crimpdeq/crimpdeq-firmware/src/hx711.rs

/// HX711 driver
///
/// A driver for the HX711 24-bit ADC commonly used with load cells.
/// This driver provides functions for reading data, calibration, and taring.
///
/// Based on [loadcell] crate.
///
/// [loadcell]: https://crates.io/crates/loadcell
use core::fmt;

use defmt::{debug, error, info, warn};
use embassy_time::{Duration, with_timeout};
use embedded_hal::delay::DelayNs;
use esp_bootloader_esp_idf::partitions::{PARTITION_TABLE_MAX_LEN, read_partition_table};
use esp_hal::{
    delay::Delay,
    gpio::{Input, Output},
};
use esp_storage::FlashStorage;

/// The absolute minimum readings. A smaller value should be clamped.
const HX711_MINIMUM: i32 = -(2i32.saturating_pow(24 - 1));
/// The absolute maximum readings. A greater value should be clamped.
const HX711_MAXIMUM: i32 = 2i32.saturating_pow(24 - 1) - 1;
/// The default delay time in microseconds for the HX711.
const HX711_DELAY_TIME_US: u32 = 1;
/// The number of bits in the HX711 reading
const HX711_DATA_BITS: usize = 24;
/// The sign bit position in the HX711 reading
const HX711_SIGN_BIT: u32 = 0x800000;
/// Timeout waiting for the HX711 data pin to signal readiness.
const HX711_READY_TIMEOUT: Duration = Duration::from_millis(500);
/// Number of readings discarded after power-up.
///
/// The first conversion after power-up uses channel A with gain 128, and the output needs
/// 4 more conversion periods to settle after the switch to the configured gain.
const HX711_SETTLE_READINGS: usize = 5;

/// Label of the data partition that stores the calibration.
const CALIBRATION_PARTITION_LABEL: &str = "calib";
/// Magic value used to validate stored calibration data.
const CALIBRATION_STORAGE_MAGIC: u32 = 0x4344_5146;
/// Storage format version for persisted calibration data.
const CALIBRATION_STORAGE_VERSION: u32 = 1;
/// Number of bytes used to store the persisted calibration blob.
const CALIBRATION_STORAGE_SIZE: usize = 16;
/// The default number of samples for taring
const DEFAULT_TARING_SAMPLES: usize = 16;
/// The default number of samples for calibration
const DEFAULT_CALIBRATION_SAMPLES: usize = 100;
/// The default calibration value.
const DEFAULT_CALIBRATION_FACTOR: f32 = 0.08;

/// Custom error type for HX711 operations
#[derive(Debug)]
pub enum Hx711Error {
    /// Flash storage error
    FlashError,
    /// Invalid calibration value
    InvalidCalibration,
    /// Timed out waiting for the HX711 to become ready.
    NotReadyTimeout,
}

impl fmt::Display for Hx711Error {
    fn fmt(&self, f: &mut fmt::Formatter<'_>) -> fmt::Result {
        match self {
            Hx711Error::FlashError => write!(f, "Flash storage error"),
            Hx711Error::InvalidCalibration => write!(f, "Invalid calibration value"),
            Hx711Error::NotReadyTimeout => write!(f, "HX711 ready timeout"),
        }
    }
}

/// The HX711 has different amplifier gain settings.
/// The choice of gain settings is controlled by writing a fixed number of
/// extra pulses after a read.
#[repr(u8)]
#[derive(Clone, Copy, Debug)]
pub enum GainMode {
    /// Amplification gain of 128 on channel A.
    A128 = 1,
    /// Amplification gain of 32 on channel B.
    B32 = 2,
    /// Amplification gain of 64 on channel A.
    A64 = 3,
}

/// HX711 24-bit ADC driver
pub struct Hx711<'d> {
    /// Data pin
    data: Input<'d>,
    /// Clock pin
    clock: Output<'d>,
    /// Delay instance
    delay: Delay,
    /// Flash storage
    flash: FlashStorage<'d>,
    /// Gain mode
    gain_mode: GainMode,
    /// Tare value
    tare_value: i32,
    /// Calibration
    calibration_factor: f32,
    /// Whether the HX711 is in power-down mode
    powered_down: bool,
}

impl<'d> Hx711<'d> {
    /// Create a new HX711 driver.
    pub fn new(
        data: Input<'d>,
        mut clock: Output<'d>,
        delay: Delay,
        flash: FlashStorage<'d>,
    ) -> Self {
        info!("HX711 initialized");
        clock.set_low();

        let mut hx711 = Self {
            data,
            clock,
            delay,
            flash,
            gain_mode: GainMode::A64,
            tare_value: 0,
            calibration_factor: 0.0,
            powered_down: false,
        };

        hx711.calibration_factor = hx711
            .get_calibration_factor()
            .unwrap_or(DEFAULT_CALIBRATION_FACTOR);

        hx711
    }

    fn calibration_storage_offset(&mut self) -> Result<u32, Hx711Error> {
        let mut table_buffer = [0u8; PARTITION_TABLE_MAX_LEN];
        match read_partition_table(&mut self.flash, &mut table_buffer) {
            Ok(table) => {
                if let Some(partition) = table
                    .iter()
                    .find(|partition| partition.label_as_str() == CALIBRATION_PARTITION_LABEL)
                {
                    if (partition.len() as usize) < CALIBRATION_STORAGE_SIZE {
                        error!("Calibration partition too small");
                        return Err(Hx711Error::FlashError);
                    }
                    return Ok(partition.offset());
                }
            }
            Err(e) => warn!("Failed to read partition table: {:?}", e),
        }

        // Updates that only flash the app keep the previous partition table, which has no
        // calibration partition. Fall back to the last flash sector: the calibration was stored
        // there before the partition existed, and the partition starts at the same offset.
        warn!("Calibration partition not found, using the last flash sector");
        let capacity = self.flash.capacity();
        let sector_size = FlashStorage::SECTOR_SIZE as usize;

        if capacity < sector_size {
            error!("Flash capacity too small for calibration storage");
            return Err(Hx711Error::FlashError);
        }

        Ok((capacity - sector_size) as u32)
    }

    fn calibration_checksum(factor_bits: u32) -> u32 {
        CALIBRATION_STORAGE_MAGIC ^ CALIBRATION_STORAGE_VERSION ^ factor_bits ^ 0xA5A5_5A5A
    }

    /// Read calibration factor from flash
    fn read_from_flash(&mut self) -> Result<f32, Hx711Error> {
        let mut bytes = [0u8; CALIBRATION_STORAGE_SIZE];
        let offset = self.calibration_storage_offset()?;

        self.flash.read(offset, &mut bytes).map_err(|_| {
            error!("Failed to read calibration factor from flash");
            Hx711Error::FlashError
        })?;

        let magic = u32::from_le_bytes(bytes[0..4].try_into().unwrap());
        let version = u32::from_le_bytes(bytes[4..8].try_into().unwrap());
        let factor_bits = u32::from_le_bytes(bytes[8..12].try_into().unwrap());
        let checksum = u32::from_le_bytes(bytes[12..16].try_into().unwrap());

        if magic != CALIBRATION_STORAGE_MAGIC || version != CALIBRATION_STORAGE_VERSION {
            info!("Calibration storage missing or version mismatch");
            return Err(Hx711Error::InvalidCalibration);
        }

        if checksum != Self::calibration_checksum(factor_bits) {
            error!("Calibration storage checksum mismatch");
            return Err(Hx711Error::InvalidCalibration);
        }

        let factor = f32::from_bits(factor_bits);
        if !Self::is_valid_calibration_factor(factor) {
            info!("Invalid calibration factor read from flash");
            return Err(Hx711Error::InvalidCalibration);
        }

        Ok(factor)
    }

    /// Check if the calibration factor is valid
    pub fn is_valid_calibration_factor(factor: f32) -> bool {
        factor.is_finite() && factor != 0.0
    }

    /// Write calibration factor to flash
    fn write_to_flash(&mut self, calibration_factor: f32) -> Result<(), Hx711Error> {
        if !Self::is_valid_calibration_factor(calibration_factor) {
            return Err(Hx711Error::InvalidCalibration);
        }

        let factor_bits = calibration_factor.to_bits();
        let checksum = Self::calibration_checksum(factor_bits);
        let mut bytes = [0u8; CALIBRATION_STORAGE_SIZE];
        bytes[0..4].copy_from_slice(&CALIBRATION_STORAGE_MAGIC.to_le_bytes());
        bytes[4..8].copy_from_slice(&CALIBRATION_STORAGE_VERSION.to_le_bytes());
        bytes[8..12].copy_from_slice(&factor_bits.to_le_bytes());
        bytes[12..16].copy_from_slice(&checksum.to_le_bytes());

        let offset = self.calibration_storage_offset()?;
        self.flash.write(offset, &bytes).map_err(|_| {
            error!("Failed to write calibration factor to flash");
            Hx711Error::FlashError
        })?;

        Ok(())
    }

    /// Update the calibration factor in memory and flash.
    pub fn update_calibration_factor(&mut self, factor: f32) -> Result<(), Hx711Error> {
        if !Self::is_valid_calibration_factor(factor) {
            error!("Invalid calibration factor: {}", factor);
            return Err(Hx711Error::InvalidCalibration);
        }

        info!("Updating calibration factor: {}", factor);
        self.write_to_flash(factor)?;

        self.calibration_factor = factor;
        Ok(())
    }

    pub fn get_calibration_factor(&mut self) -> Result<f32, Hx711Error> {
        // Get the calibration factor from the NVS flash storage.
        match self.read_from_flash() {
            Ok(factor) => {
                info!("Calibration factor read from flash: {:?}", factor);
                Ok(factor)
            }
            Err(Hx711Error::InvalidCalibration) => {
                info!("Using default calibration factor");
                Ok(DEFAULT_CALIBRATION_FACTOR)
            }
            Err(e) => Err(e),
        }
    }

    /// Get the current calibration factor.
    pub fn current_calibration_factor(&self) -> f32 {
        self.calibration_factor
    }

    /// Set the default calibration factor.
    pub fn default_calibration_factor(&mut self) -> Result<(), Hx711Error> {
        debug!("Restoring default calibration factor");
        self.write_to_flash(DEFAULT_CALIBRATION_FACTOR)?;
        self.calibration_factor = DEFAULT_CALIBRATION_FACTOR;
        Ok(())
    }

    /// Put the HX711 into its low-power power-down mode.
    ///
    /// The clock pad is held high so the HX711 stays powered down during deep sleep,
    /// when the digital domain no longer drives the pin.
    pub fn power_down(&mut self) {
        debug!("Powering down HX711");
        self.clock.set_high();
        self.clock.set_pad_hold(true);
        self.delay.delay_us(80);
        self.powered_down = true;
    }

    /// Wake the HX711 back up after power-down.
    pub fn power_up(&mut self) {
        debug!("Powering up HX711");
        self.clock.set_pad_hold(false);
        self.clock.set_low();
        self.delay.delay_us(80);
        self.powered_down = false;
    }

    /// Returns whether the HX711 is in power-down mode.
    pub fn is_powered_down(&self) -> bool {
        self.powered_down
    }

    /// Power the HX711 up if needed and wait until its readings are usable.
    ///
    /// If settling fails, the HX711 is powered down again so the next call retries it.
    pub async fn wake(&mut self) -> Result<(), Hx711Error> {
        if self.powered_down {
            self.power_up();
            if let Err(e) = self.settle().await {
                self.power_down();
                return Err(e);
            }
        }
        Ok(())
    }

    /// Discards the readings taken before the configured gain applies and the output settles.
    pub async fn settle(&mut self) -> Result<(), Hx711Error> {
        debug!(
            "Discarding {} HX711 settling readings",
            HX711_SETTLE_READINGS
        );
        for _ in 0..HX711_SETTLE_READINGS {
            self.wait_for_ready().await?;
            self.read_raw();
        }
        Ok(())
    }

    /// Reads a single bit from the data pin.
    #[inline]
    fn read_data_bit(&mut self) -> bool {
        self.clock.set_high();
        self.delay.delay_us(HX711_DELAY_TIME_US);

        let bit = self.data.is_high();

        self.clock.set_low();
        self.delay.delay_us(HX711_DELAY_TIME_US);

        bit
    }

    /// Toggles the clock pin to prepare for the next gain mode.
    fn send_gain_pulses(&mut self) {
        critical_section::with(|_| {
            let pulses = self.gain_mode as u8;
            for _ in 0..pulses {
                self.clock.set_high();
                self.delay.delay_us(HX711_DELAY_TIME_US);
                self.clock.set_low();
                self.delay.delay_us(HX711_DELAY_TIME_US);
            }
        });
    }

    /// Sets the gain mode for the next reading.
    pub fn set_gain_mode(&mut self, gain_mode: GainMode) {
        self.gain_mode = gain_mode;
    }

    /// Gets the current gain mode.
    pub fn gain_mode(&self) -> GainMode {
        self.gain_mode
    }

    /// Reads 24 bits from the HX711 within a critical section.
    fn read_raw(&mut self) -> i32 {
        let value = critical_section::with(|_| {
            let mut result: u32 = 0;
            for _ in 0..HX711_DATA_BITS {
                result = (result << 1) | (self.read_data_bit() as u32);
            }
            result
        });

        self.send_gain_pulses();

        // Handle sign extension for 24-bit signed values
        let extended_value = if value & HX711_SIGN_BIT != 0 {
            value | 0xFF000000 // Negative value, extend the sign bit
        } else {
            value // Positive value, no change
        };

        // Clamp to valid range and return as signed 32-bit
        (extended_value as i32).clamp(HX711_MINIMUM, HX711_MAXIMUM)
    }

    /// Waits until the data is ready to be read.
    async fn wait_for_ready(&mut self) -> Result<(), Hx711Error> {
        with_timeout(HX711_READY_TIMEOUT, self.data.wait_for_low())
            .await
            .map_err(|_| {
                error!("Timed out waiting for HX711 ready signal");
                Hx711Error::NotReadyTimeout
            })
    }

    /// Takes multiple samples and returns the average
    async fn take_samples(&mut self, num_samples: usize) -> Result<f32, Hx711Error> {
        let mut total: i64 = 0;

        for _ in 0..num_samples {
            self.wait_for_ready().await?;
            total += i64::from(self.read_raw());
        }

        Ok((total as f64 / num_samples as f64) as f32)
    }

    /// Tares the sensor by measuring the average of several readings.
    pub async fn tare(&mut self) -> Result<(), Hx711Error> {
        debug!("Taring the scale");
        let average = self.take_samples(DEFAULT_TARING_SAMPLES).await?;
        self.tare_value = average as i32;
        debug!("Tare value set to: {}", self.tare_value);
        Ok(())
    }

    /// Reads a raw value without calibration
    pub async fn read_raw_value(&mut self) -> Result<i32, Hx711Error> {
        self.wait_for_ready().await?;
        Ok(self.read_raw())
    }

    /// Reads a tared raw value (raw value minus tare value)
    pub async fn read_tared(&mut self) -> Result<i32, Hx711Error> {
        self.wait_for_ready().await?;
        Ok(self.read_raw() - self.tare_value)
    }

    /// Reads a calibrated value, in kg.
    pub async fn read_calibrated(&mut self) -> Result<f32, Hx711Error> {
        let raw_tared = self.read_tared().await?;
        let calibrated_value = (raw_tared as f32) * self.calibration_factor;
        // Convert to kg
        Ok(calibrated_value / 1000.0)
    }

    /// Perform two-point calibration with a known target weight
    ///
    /// This method collects raw values for calibration by taking multiple samples
    /// and averaging them for stability.
    ///
    /// Returns the average raw value for the calibration point.
    pub async fn perform_calibration(&mut self) -> Result<f32, Hx711Error> {
        // Take multiple readings and average them for stability using raw values.
        let average_value = self.take_samples(DEFAULT_CALIBRATION_SAMPLES).await?;
        debug!("Calibration point collected: {}", average_value);

        Ok(average_value)
    }

    /// Apply multi-point calibration using the collected calibration points.
    ///
    /// This method calculates and applies a best-fit calibration factor
    /// based on the provided (raw_value, weight) pairs.
    ///
    /// Returns true if calibration was successfully applied, false otherwise.
    pub fn apply_multi_point_calibration(&mut self, calibration_points: &[(f32, f32)]) -> bool {
        if calibration_points.len() < 2 {
            error!("Calibration requires at least two points");
            return false;
        }

        let is_valid = |(raw_value, weight): &&(f32, f32)| {
            raw_value.is_finite() && weight.is_finite() && *weight >= 0.0
        };
        for (raw_value, weight) in calibration_points.iter().filter(|point| !is_valid(point)) {
            error!(
                "Skipping invalid calibration point raw={}, weight={}",
                raw_value, weight
            );
        }

        // Incoming calibration weights are expressed in kg, while calibration_factor operates on
        // grams before read_calibrated() converts back to kg.
        let valid_points = || {
            calibration_points
                .iter()
                .filter(is_valid)
                .map(|(raw_value, weight)| (f64::from(*raw_value), f64::from(*weight) * 1000.0))
        };

        let valid_count = valid_points().count();
        if valid_count < 2 {
            error!("Calibration requires at least two valid points");
            return false;
        }

        // Least-squares slope around the mean, so no single point anchors the fit.
        let (sum_raw, sum_weight) = valid_points()
            .fold((0.0, 0.0), |(sum_raw, sum_weight), (raw, weight)| {
                (sum_raw + raw, sum_weight + weight)
            });
        let mean_raw = sum_raw / valid_count as f64;
        let mean_weight = sum_weight / valid_count as f64;
        let (sum_delta_raw_weight, sum_delta_raw_sq) = valid_points().fold(
            (0.0, 0.0),
            |(sum_delta_raw_weight, sum_delta_raw_sq), (raw, weight)| {
                let delta_raw = raw - mean_raw;
                (
                    sum_delta_raw_weight + delta_raw * (weight - mean_weight),
                    sum_delta_raw_sq + delta_raw * delta_raw,
                )
            },
        );

        if sum_delta_raw_sq < f64::EPSILON {
            error!("Invalid calibration - points are too close together");
            return false;
        }

        let scale_factor = (sum_delta_raw_weight / sum_delta_raw_sq) as f32;
        match self.update_calibration_factor(scale_factor) {
            Ok(_) => {
                info!(
                    "Calibration factor successfully applied: {:?}",
                    scale_factor
                );
                true
            }
            Err(e) => {
                error!(
                    "Failed to apply calibration factor: {:?}",
                    defmt::Debug2Format(&e)
                );
                false
            }
        }
    }
}
