crimpdeq/crimpdeq-firmware/src/progressor.rs

/// Progressor data types
///
/// See [Tindeq API documentation] for more information
///
/// [Tindeq API documentation]: https://tindeq.com/progressor_api/
use defmt::{Format, error, info, warn};
use embassy_sync::{
    blocking_mutex::raw::{CriticalSectionRawMutex, NoopRawMutex},
    channel::Channel,
};
use esp_hal::time;
use trouble_host::types::gatt_traits::{AsGatt, FromGatt, FromGattError};

/// Size of the channel used to send data points
const DATA_POINT_COMMAND_CHANNEL_SIZE: usize = 80;
/// Channel used to send data points
pub type DataPointChannel = Channel<NoopRawMutex, DataPoint, DATA_POINT_COMMAND_CHANNEL_SIZE>;
/// Number of load cell commands that can wait for the measurement task.
const LOAD_CELL_COMMAND_QUEUE_SIZE: usize = 4;
/// Queue of one-shot commands for the measurement task.
pub static LOAD_CELL_COMMANDS: Channel<
    CriticalSectionRawMutex,
    LoadCellCommand,
    LOAD_CELL_COMMAND_QUEUE_SIZE,
> = Channel::new();

/// Number of samples packed into each BLE measurement packet.
pub const SAMPLES_PER_PACKET: usize = 5;
/// Size in bytes of one packed weight measurement (f32 weight + u32 timestamp).
const WEIGHT_MEASUREMENT_SIZE: usize = 8;
/// Maximum size of the payload written to the Control Point characteristic.
pub const CONTROL_POINT_MAX_PAYLOAD_SIZE: usize = 10;
/// Batch of weight measurements sent in a single BLE packet.
pub type WeightMeasurementBatch = arrayvec::ArrayVec<(f32, u32), SAMPLES_PER_PACKET>;
/// Maximum size of the payload sent in a Data Point notification.
pub const DATA_POINT_MAX_PAYLOAD_SIZE: usize = SAMPLES_PER_PACKET * WEIGHT_MEASUREMENT_SIZE;

/// Number of bytes in the device ID
const DEVICE_ID_SIZE: usize = 6;
/// Maximum number of calibration points to store
pub const MAX_CALIBRATION_POINTS: usize = 20;

/// Calibration point storing raw value and known weight
pub type CalibrationPoint = (f32, f32);

/// Status of the weight measurement task
#[derive(Copy, Debug, Clone, PartialEq)]
pub enum MeasurementTaskStatus {
    /// Measurements are enabled
    Enabled,
    /// Measurements are disabled
    Disabled,
}

/// One-shot command handled by the measurement task.
#[derive(Copy, Clone, Debug, PartialEq, Format)]
pub enum LoadCellCommand {
    /// Taring the scale (used in ClimbHarder App)
    Tare,
    /// Adds a calibration point with the known weight in kg
    Calibrate(f32),
    /// Restores default calibration values
    DefaultCalibration,
    /// Get the calibration values
    GetCalibration,
}

impl LoadCellCommand {
    /// Returns whether this command needs readings from the load cell.
    pub fn uses_load_cell(self) -> bool {
        matches!(self, Self::Tare | Self::Calibrate(_))
    }
}

/// Reason why the device is transitioning to sleep.
#[derive(Copy, Clone, Debug, PartialEq, Format)]
pub enum SleepReason {
    /// No user or BLE activity has been observed for too long.
    IdleTimeout,
    /// The client sent the Shutdown command.
    Shutdown,
    /// The battery is too low to keep the 3V3 rail regulated.
    LowBattery,
}

/// Sleep transition state.
#[derive(Copy, Clone, Debug, PartialEq, Format)]
pub enum SleepState {
    /// Device is fully awake.
    Awake,
    /// Deep sleep has been requested and peripherals are shutting down.
    Requested(SleepReason),
    /// Peripherals are powered down and deep sleep can be entered.
    Ready(SleepReason),
}

/// Peripheral that must acknowledge shutdown before deep sleep starts.
#[derive(Copy, Clone, Debug, PartialEq)]
pub enum SleepReadySource {
    Measurement,
    StatusLed,
}

/// Device state management
#[derive(Debug, Clone, PartialEq)]
pub struct DeviceState {
    /// Measurement status
    pub measurement_status: MeasurementTaskStatus,
    /// Start time of the measurement in microseconds
    pub start_time: u32,
    /// Calibration points (raw value, weight)
    pub calibration_points: [CalibrationPoint; MAX_CALIBRATION_POINTS],
    /// Number of calibration points currently stored
    pub calibration_point_count: usize,
    /// Battery voltage in millivolts
    pub battery_voltage: u32,
    /// Timestamp of the last user-visible activity.
    pub last_activity_time_ms: u32,
    /// Whether BLE is currently connected.
    pub ble_connected: bool,
    /// Current sleep transition state.
    pub sleep_state: SleepState,
    /// Whether the measurement task has powered down its peripherals for sleep.
    pub sleep_measurement_ready: bool,
    /// Whether the status LED has been explicitly turned off for sleep.
    pub sleep_status_led_ready: bool,
    /// Whether the client asked to turn the device off once it disconnects.
    pub shutdown_requested: bool,
}

impl Default for DeviceState {
    fn default() -> Self {
        Self::new()
    }
}

impl DeviceState {
    /// Create the state used after boot.
    pub const fn new() -> Self {
        Self {
            measurement_status: MeasurementTaskStatus::Disabled,
            start_time: 0,
            calibration_points: [(0.0, 0.0); MAX_CALIBRATION_POINTS],
            calibration_point_count: 0,
            battery_voltage: 4300,
            last_activity_time_ms: 0,
            ble_connected: false,
            sleep_state: SleepState::Awake,
            sleep_measurement_ready: false,
            sleep_status_led_ready: false,
            shutdown_requested: false,
        }
    }

    fn now_ms() -> u32 {
        (time::Instant::now().duration_since_epoch()).as_millis() as u32
    }

    fn cancel_idle_sleep_request(&mut self) {
        match self.sleep_state {
            SleepState::Requested(SleepReason::IdleTimeout)
            | SleepState::Ready(SleepReason::IdleTimeout) => {
                self.sleep_state = SleepState::Awake;
                self.sleep_measurement_ready = false;
                self.sleep_status_led_ready = false;
            }
            // Activity does not cancel a shutdown or a low battery sleep.
            SleepState::Requested(_) | SleepState::Ready(_) | SleepState::Awake => {}
        }
    }

    /// Record user-visible activity so idle sleep can be postponed.
    pub fn record_activity(&mut self) {
        self.cancel_idle_sleep_request();
        self.last_activity_time_ms = Self::now_ms();
    }

    /// Start a measurement
    pub fn start_measurement(&mut self) {
        self.record_activity();
        self.start_time = (time::Instant::now().duration_since_epoch()).as_micros() as u32;
        self.measurement_status = MeasurementTaskStatus::Enabled;
    }

    /// Stop the current measurement
    pub fn stop_measurement(&mut self) {
        self.record_activity();
        self.measurement_status = MeasurementTaskStatus::Disabled;
    }

    /// Queue a command for the measurement task.
    fn queue_load_cell_command(&mut self, command: LoadCellCommand) {
        self.record_activity();
        if LOAD_CELL_COMMANDS.try_send(command).is_err() {
            warn!("Load cell command queue full, dropping {:?}", command);
        }
    }

    /// Start taring process
    pub fn tare(&mut self) {
        self.queue_load_cell_command(LoadCellCommand::Tare);
    }

    /// Add a calibration point with the given weight
    pub fn calibrate(&mut self, weight: f32) {
        self.queue_load_cell_command(LoadCellCommand::Calibrate(weight));
    }

    pub fn get_calibration(&mut self) {
        self.queue_load_cell_command(LoadCellCommand::GetCalibration);
    }

    /// Reset to default calibration
    pub fn reset_calibration(&mut self) {
        self.queue_load_cell_command(LoadCellCommand::DefaultCalibration);
    }

    /// Mark BLE as connected.
    pub fn on_ble_connected(&mut self) {
        self.ble_connected = true;
        self.record_activity();
    }

    /// Mark BLE as disconnected and drop the commands of the closed connection.
    pub fn on_ble_disconnected(&mut self) {
        LOAD_CELL_COMMANDS.clear();
        self.ble_connected = false;
        self.record_activity();
        if self.shutdown_requested {
            self.request_sleep(SleepReason::Shutdown);
        }
    }

    /// Returns true when BLE is currently connected.
    pub fn is_ble_connected(&self) -> bool {
        self.ble_connected
    }

    /// Get elapsed inactivity time in milliseconds.
    pub fn get_inactivity_elapsed_ms(&self) -> u32 {
        Self::now_ms().wrapping_sub(self.last_activity_time_ms)
    }

    /// Request deep sleep. The measurement and LED tasks will power down peripherals first.
    pub fn request_sleep(&mut self, reason: SleepReason) {
        if self.sleep_state == SleepState::Awake {
            LOAD_CELL_COMMANDS.clear();
            self.measurement_status = MeasurementTaskStatus::Disabled;
            self.sleep_measurement_ready = false;
            self.sleep_status_led_ready = false;
            self.sleep_state = SleepState::Requested(reason);
        }
    }

    /// Reset runtime state to the same awake/disconnected state used after boot.
    pub fn reset_to_initial_state(&mut self) {
        let battery_voltage = self.battery_voltage;
        *self = Self {
            battery_voltage,
            ..Self::default()
        };
        self.on_ble_disconnected();
    }

    /// Mark that one peripheral is powered down and deep sleep can start when all are ready.
    pub fn mark_sleep_ready(&mut self, source: SleepReadySource) {
        if let SleepState::Requested(reason) = self.sleep_state {
            match source {
                SleepReadySource::Measurement => self.sleep_measurement_ready = true,
                SleepReadySource::StatusLed => self.sleep_status_led_ready = true,
            }

            if self.sleep_measurement_ready && self.sleep_status_led_ready {
                self.sleep_state = SleepState::Ready(reason);
            }
        }
    }
}

/// Progressor Commands
#[derive(Debug, Clone, Copy)]
/// Commands that Tindeq app can send to the device
// Source: Tindeq API documentation and https://github.com/blims/Tindeq-Progressor-API/blob/78a0bd244303589d0c773ee15ede53e0299712ee/progressor_client.py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
pub enum ControlOpCode {
    /// Command used to zero weight when no load is applied
    TareScale = 0x64,
    /// Start continuous measurement. Sample rate is 80Hz
    StartMeasurement = 0x65,
    /// Stop weight measurement. This should be done before sampling the battery voltage
    StopMeasurement = 0x66,
    /// Start peak RFD measurement
    // TODO: Implement it
    StartPeakRFDMeasurement = 0x67,
    /// Start peak RFD measurement series
    // TODO: Implement it
    StartPeakRFDMeasurementSeries = 0x68,
    /// Adds a calibration point
    AddCalibrationPoint = 0x69,
    /// Save calibration
    // TODO: Implement it
    SaveCalibration = 0x6A,
    /// Get the error information
    // TODO: Implement it
    GetErrorInformation = 0x6C,
    /// Clear the error information
    // TODO: Implement it
    ClearErrorInformation = 0x6D,
    /// Turn the Progressor off (enter sleep mode)
    Shutdown = 0x6E,
    /// Measures the battery voltage in millivolts
    SampleBattery = 0x6F,
    /// Get the Progressor ID
    GetProgressorId = 0x70,
    /// Get the application version
    GetAppVersion = 0x6B,
    /// Get the calibration values
    // Custom command, no part of Tindeq API
    GetCalibration = 0x72,
    /// Default calibration
    // Custom command, no part of Tindeq API
    DefaultCalibration = 0x74,
}

impl ControlOpCode {
    /// Returns whether this command should reset the idle timer.
    pub fn counts_as_activity(self) -> bool {
        !matches!(self, ControlOpCode::SampleBattery)
    }

    /// Process the control operation.
    ///
    /// Returns an immediate response packet when the command requires one.
    pub fn process(self, data: &[u8], device_state: &mut DeviceState) -> Option<DataPoint> {
        match self {
            ControlOpCode::TareScale => {
                device_state.tare();
                None
            }
            ControlOpCode::StartMeasurement => {
                device_state.start_measurement();
                None
            }
            ControlOpCode::StopMeasurement => {
                device_state.stop_measurement();
                None
            }
            ControlOpCode::GetAppVersion => {
                let response = ResponseCode::AppVersion(env!("DEVICE_VERSION_NUMBER").as_bytes());
                info!("AppVersion: {:#x}", response);
                Some(DataPoint::from(response))
            }
            ControlOpCode::GetProgressorId => {
                /// Number of hex characters needed per byte (2 hex chars = 1 byte)
                const HEX_CHARS_PER_BYTE: usize = 2;
                /// Hex radix for parsing hex strings
                const HEX_RADIX: u32 = 16;

                let device_id = env!("DEVICE_ID");
                let mut bytes = [0u8; DEVICE_ID_SIZE];
                for (i, byte) in bytes.iter_mut().enumerate() {
                    let char_pos = i * HEX_CHARS_PER_BYTE;
                    let next_char_pos = char_pos + HEX_CHARS_PER_BYTE;
                    if next_char_pos <= device_id.len()
                        && let Ok(parsed_byte) =
                            u8::from_str_radix(&device_id[char_pos..next_char_pos], HEX_RADIX)
                    {
                        *byte = parsed_byte;
                    }
                }
                let response = ResponseCode::ProgressorId(bytes);
                info!("ProgressorId: {:?}", response);
                Some(DataPoint::from(response))
            }
            ControlOpCode::GetCalibration => {
                info!("GetCalibration requested");
                device_state.get_calibration();
                None
            }
            ControlOpCode::AddCalibrationPoint => {
                if data.len() < 5 {
                    error!("AddCalibrationPoint: Invalid data length");
                    return None;
                }

                let weight = match data[1..5].try_into() {
                    Ok(bytes) => f32::from_le_bytes(bytes),
                    Err(e) => {
                        error!("Failed to parse calibration point data: {:?}", e);
                        return None;
                    }
                };

                if !weight.is_finite() || weight < 0.0 {
                    error!("AddCalibrationPoint: Invalid weight {}", weight);
                    return None;
                }

                device_state.calibrate(weight);
                info!(
                    "Received AddCalibrationPoint command with measurement: {}",
                    weight
                );
                None
            }
            ControlOpCode::DefaultCalibration => {
                device_state.reset_calibration();
                None
            }
            ControlOpCode::SampleBattery => {
                let voltage = device_state.battery_voltage;
                let response = ResponseCode::SampleBatteryVoltage(voltage);
                info!("SampleBattery: {:?}", response);
                Some(DataPoint::from(response))
            }
            ControlOpCode::Shutdown => {
                info!("Shutdown command received, entering deep sleep after disconnect");
                device_state.reset_to_initial_state();
                device_state.shutdown_requested = true;
                None
            }
            // Currently unimplemented operations
            ControlOpCode::StartPeakRFDMeasurement
            | ControlOpCode::StartPeakRFDMeasurementSeries
            | ControlOpCode::SaveCalibration
            | ControlOpCode::ClearErrorInformation
            | ControlOpCode::GetErrorInformation => None,
        }
    }
}

impl TryFrom<u8> for ControlOpCode {
    type Error = ();

    fn try_from(op_code: u8) -> Result<Self, Self::Error> {
        match op_code {
            0x64 => Ok(ControlOpCode::TareScale),
            0x65 => Ok(ControlOpCode::StartMeasurement),
            0x66 => Ok(ControlOpCode::StopMeasurement),
            0x69 => Ok(ControlOpCode::AddCalibrationPoint),
            0x6E => Ok(ControlOpCode::Shutdown),
            0x6F => Ok(ControlOpCode::SampleBattery),
            0x70 => Ok(ControlOpCode::GetProgressorId),
            0x6B => Ok(ControlOpCode::GetAppVersion),
            0x72 => Ok(ControlOpCode::GetCalibration),
            0x74 => Ok(ControlOpCode::DefaultCalibration),
            0x6C => Ok(ControlOpCode::GetErrorInformation),
            0x6D => Ok(ControlOpCode::ClearErrorInformation),
            0x67 => Ok(ControlOpCode::StartPeakRFDMeasurement),
            0x68 => Ok(ControlOpCode::StartPeakRFDMeasurementSeries),
            0x6A => Ok(ControlOpCode::SaveCalibration),
            _ => Err(()),
        }
    }
}

impl Format for ControlOpCode {
    fn format(&self, fmt: defmt::Formatter) {
        match self {
            ControlOpCode::TareScale => defmt::write!(fmt, "TareScale"),
            ControlOpCode::StartMeasurement => defmt::write!(fmt, "StartMeasurement"),
            ControlOpCode::StopMeasurement => defmt::write!(fmt, "StopMeasurement"),
            ControlOpCode::GetAppVersion => defmt::write!(fmt, "GetAppVersion"),
            ControlOpCode::Shutdown => defmt::write!(fmt, "Shutdown"),
            ControlOpCode::SampleBattery => defmt::write!(fmt, "SampleBattery"),
            ControlOpCode::GetProgressorId => defmt::write!(fmt, "GetProgressorId"),
            ControlOpCode::GetCalibration => defmt::write!(fmt, "GetCalibration"),
            ControlOpCode::AddCalibrationPoint => defmt::write!(fmt, "AddCalibrationPoint"),
            ControlOpCode::DefaultCalibration => defmt::write!(fmt, "DefaultCalibration"),
            ControlOpCode::StartPeakRFDMeasurement => defmt::write!(fmt, "StartPeakRFDMeasurement"),
            ControlOpCode::StartPeakRFDMeasurementSeries => {
                defmt::write!(fmt, "StartPeakRFDMeasurementSeries")
            }
            ControlOpCode::SaveCalibration => defmt::write!(fmt, "SaveCalibration"),
            ControlOpCode::GetErrorInformation => defmt::write!(fmt, "GetErrorInformation"),
            ControlOpCode::ClearErrorInformation => defmt::write!(fmt, "ClearErrorInformation"),
        }
    }
}

/// Data point characteristic is where we receive data from the Progressor
#[derive(Debug, Clone)]
#[repr(C, packed)]
pub struct DataPoint {
    /// Response code
    pub(crate) response_code: u8,
    /// Length of the data
    pub(crate) length: u8,
    /// Data
    pub(crate) value: [u8; DATA_POINT_MAX_PAYLOAD_SIZE],
}

impl AsGatt for DataPoint {
    const MIN_SIZE: usize = 2;
    const MAX_SIZE: usize = DATA_POINT_MAX_PAYLOAD_SIZE + 2; // +2 for response_code and length

    fn as_gatt(&self) -> &[u8] {
        let len = (self.length as usize).min(DATA_POINT_MAX_PAYLOAD_SIZE);
        unsafe { core::slice::from_raw_parts(self as *const DataPoint as *const u8, 2 + len) }
    }
}

impl FromGatt for DataPoint {
    fn from_gatt(data: &[u8]) -> Result<Self, FromGattError> {
        if data.len() < 2 || data.len() > Self::MAX_SIZE {
            return Err(FromGattError::InvalidLength);
        }

        let response_code = data[0];
        let length = data[1] as usize;
        if length > DATA_POINT_MAX_PAYLOAD_SIZE || data.len() != 2 + length {
            return Err(FromGattError::InvalidLength);
        }

        Ok(DataPoint::new(response_code, data[1], &data[2..]))
    }
}

impl Default for DataPoint {
    fn default() -> Self {
        Self {
            response_code: 0,
            length: 0,
            value: [0; DATA_POINT_MAX_PAYLOAD_SIZE],
        }
    }
}

impl DataPoint {
    /// Create a new data point with specified response code, length and data
    pub fn new(response_code: u8, length: u8, data: &[u8]) -> Self {
        let mut value = [0; DATA_POINT_MAX_PAYLOAD_SIZE];
        let max_len = length.min(DATA_POINT_MAX_PAYLOAD_SIZE as u8) as usize;
        let copy_len = max_len.min(data.len());
        if copy_len > 0 {
            value[..copy_len].copy_from_slice(&data[..copy_len]);
        }

        Self {
            response_code,
            length: copy_len as u8,
            value,
        }
    }

    /// Send data point to the channel.
    pub async fn send(self, channel: &'static DataPointChannel) {
        channel.send(self).await;
    }

    /// Create a weight measurement data point
    pub fn weight_measurement(measurements: WeightMeasurementBatch) -> Self {
        Self::from(ResponseCode::WeightMeasurement(measurements))
    }
}

impl Format for DataPoint {
    fn format(&self, fmt: defmt::Formatter) {
        let len = (self.length as usize).min(DATA_POINT_MAX_PAYLOAD_SIZE);
        defmt::write!(
            fmt,
            "Code: {}, Length: {}, Data: {:x}",
            self.response_code,
            self.length,
            &self.value[0..len]
        );
    }
}

impl From<ResponseCode> for DataPoint {
    fn from(response_code: ResponseCode) -> Self {
        Self {
            response_code: response_code.op_code(),
            length: response_code.length(),
            value: response_code.value(),
        }
    }
}

/// Data point response code
#[derive(Clone, Debug)]
#[repr(u8)]
/// Response codes that the device can send to the Tindeq app
// Source: Tindeq API documentation and https://github.com/blims/Tindeq-Progressor-API/blob/78a0bd244303589d0c773ee15ede53e0299712ee/progressor_client.py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
pub enum ResponseCode {
    /// Response to battery voltage sampling command
    SampleBatteryVoltage(u32),
    /// Each measurement is sent together with a timestamp where the timestamp is the number of microseconds since the measurement was started
    WeightMeasurement(WeightMeasurementBatch),
    /// Calibration factor response
    CalibrationFactor(f32),
    /// Calibration point response (raw value, weight)
    CalibrationPoint(f32, f32),
    /// Low power warning indicating that the battery is empty. The Progressor will turn itself off after sending this warning
    LowPowerWarning,
    /// Response to app version request command
    AppVersion(&'static [u8]),
    /// Response to progressor ID request command
    ProgressorId([u8; DEVICE_ID_SIZE]),
    /// RFD peak response.
    // TODO: Implement it
    RfdPeak,
    /// RFD peak series response.
    // TODO: Implement it
    RfdPeakSeries,
}

impl Format for ResponseCode {
    fn format(&self, fmt: defmt::Formatter) {
        match self {
            ResponseCode::SampleBatteryVoltage(voltage) => {
                defmt::write!(fmt, "SampleBatteryVoltage: {}", voltage)
            }
            ResponseCode::WeightMeasurement(measurements) => {
                defmt::write!(fmt, "WeightMeasurement: {} points", measurements.len())
            }
            ResponseCode::CalibrationFactor(factor) => {
                defmt::write!(fmt, "CalibrationFactor: {}", factor)
            }
            ResponseCode::CalibrationPoint(raw, weight) => {
                defmt::write!(fmt, "CalibrationPoint: Raw: {}, Weight: {}", raw, weight)
            }
            ResponseCode::LowPowerWarning => defmt::write!(fmt, "LowPowerWarning"),
            ResponseCode::AppVersion(version) => defmt::write!(fmt, "AppVersion: {:x}", version),
            ResponseCode::ProgressorId(id) => defmt::write!(fmt, "ProgressorId: {:x}", id),
            ResponseCode::RfdPeak => defmt::write!(fmt, "RfdPeak"),
            ResponseCode::RfdPeakSeries => defmt::write!(fmt, "RfdPeakSeries"),
        }
    }
}

impl ResponseCode {
    /// Get the operation code for this response
    fn op_code(&self) -> u8 {
        match self {
            ResponseCode::SampleBatteryVoltage(..)
            | ResponseCode::AppVersion(..)
            | ResponseCode::ProgressorId(..) => 0x00,
            ResponseCode::WeightMeasurement(..) => 0x01,
            ResponseCode::RfdPeak => 0x02,
            ResponseCode::RfdPeakSeries => 0x03,
            ResponseCode::LowPowerWarning => 0x04,
            ResponseCode::CalibrationFactor(..) => 0x05,
            ResponseCode::CalibrationPoint(..) => 0x06,
        }
    }

    /// Get the length of the data for this response
    fn length(&self) -> u8 {
        match self {
            ResponseCode::SampleBatteryVoltage(..) => 4,
            ResponseCode::WeightMeasurement(measurements) => {
                (measurements.len() * WEIGHT_MEASUREMENT_SIZE) as u8
            }
            ResponseCode::CalibrationFactor(..) => 4,
            ResponseCode::CalibrationPoint(..) => 8,
            ResponseCode::LowPowerWarning => 0,
            ResponseCode::AppVersion(version) => {
                version.len().min(DATA_POINT_MAX_PAYLOAD_SIZE) as u8
            }
            ResponseCode::ProgressorId(..) => DEVICE_ID_SIZE as u8,
            ResponseCode::RfdPeak => 0,
            ResponseCode::RfdPeakSeries => 0,
        }
    }

    /// Get the value bytes for this response
    fn value(&self) -> [u8; DATA_POINT_MAX_PAYLOAD_SIZE] {
        let mut value = [0; DATA_POINT_MAX_PAYLOAD_SIZE];
        match self {
            ResponseCode::SampleBatteryVoltage(voltage) => {
                value[0..4].copy_from_slice(&voltage.to_le_bytes());
            }
            ResponseCode::WeightMeasurement(measurements) => {
                for (i, (weight, timestamp)) in measurements.iter().enumerate() {
                    let offset = i * WEIGHT_MEASUREMENT_SIZE;
                    value[offset..offset + 4].copy_from_slice(&weight.to_le_bytes());
                    value[offset + 4..offset + WEIGHT_MEASUREMENT_SIZE]
                        .copy_from_slice(&timestamp.to_le_bytes());
                }
            }
            ResponseCode::CalibrationFactor(factor) => {
                value[0..4].copy_from_slice(&factor.to_le_bytes());
            }
            ResponseCode::CalibrationPoint(raw_value, weight) => {
                value[0..4].copy_from_slice(&raw_value.to_le_bytes());
                value[4..8].copy_from_slice(&weight.to_le_bytes());
            }
            ResponseCode::LowPowerWarning => (),
            ResponseCode::ProgressorId(id) => {
                // Reverse the bytes as they are LE
                let mut reversed = *id;
                reversed.reverse();
                value[..DEVICE_ID_SIZE].copy_from_slice(&reversed);
            }
            ResponseCode::AppVersion(version) => {
                let len = version.len().min(DATA_POINT_MAX_PAYLOAD_SIZE);
                value[0..len].copy_from_slice(&version[0..len]);
            }
            ResponseCode::RfdPeak => {
                warn!("RfdPeak response not implemented");
            }
            ResponseCode::RfdPeakSeries => {
                warn!("RfdPeakSeries response not implemented");
            }
        };
        value
    }
}
